skyphose/deckblock/photos/IMG_3814.jpeg

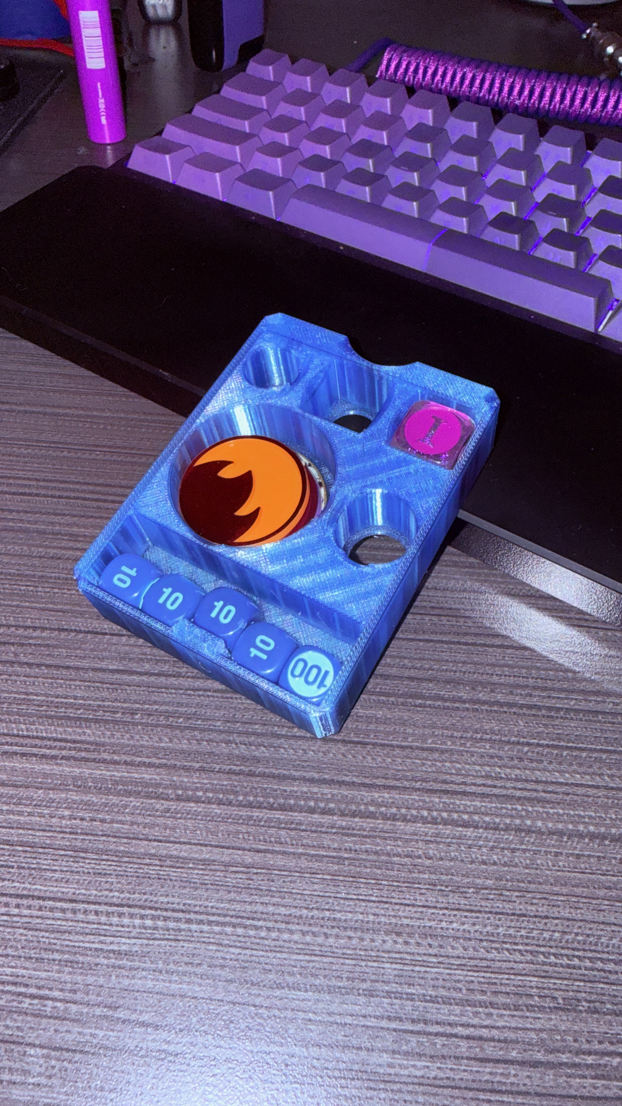
photos/IMG_3814.jpeg
