skyphose/deckblock/photos/IMG_3815.jpeg

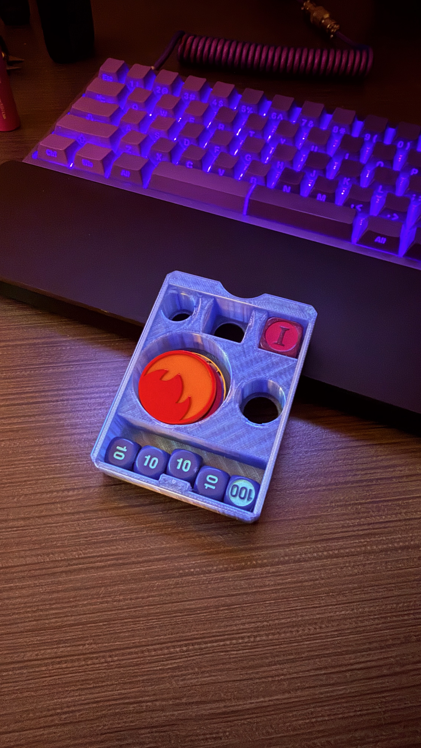
photos/IMG_3815.jpeg
