skyphose/deckblock/photos/IMG_3816.jpeg

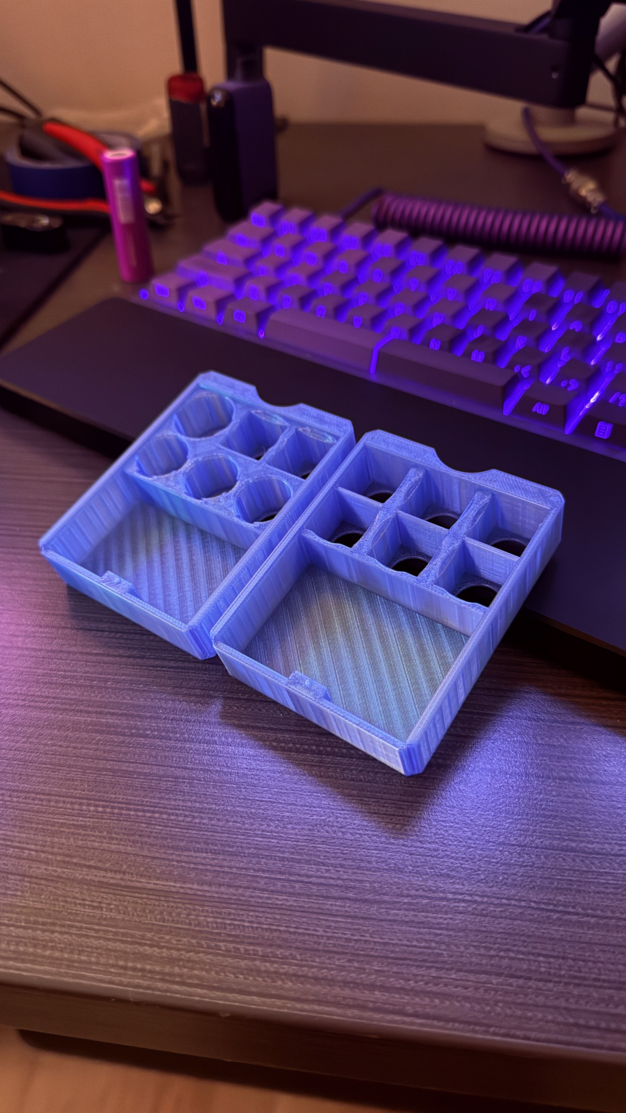
photos/IMG_3816.jpeg
