skyphose/deckblock/photos/IMG_3817.jpeg

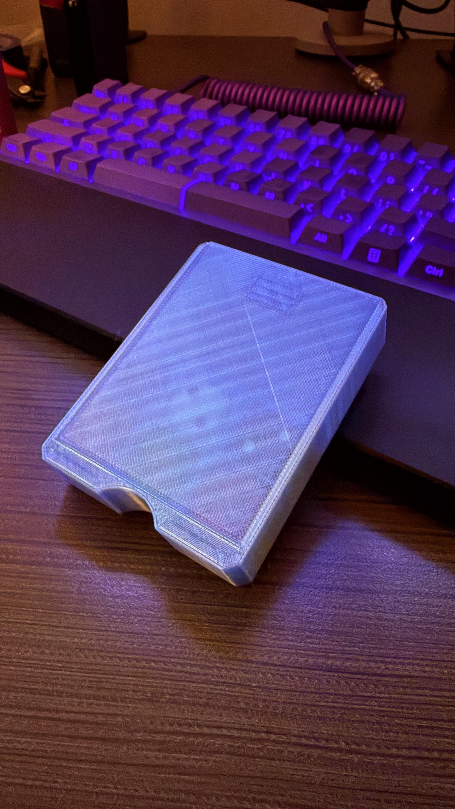
photos/IMG_3817.jpeg
