skyphose/deckblock/photos/IMG_3818.jpeg

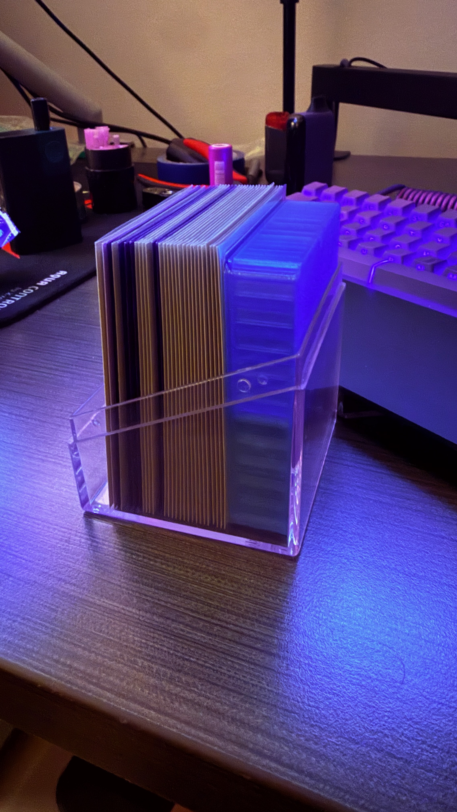
photos/IMG_3818.jpeg
