skyphose/deckblock/photos/IMG_3819.jpeg

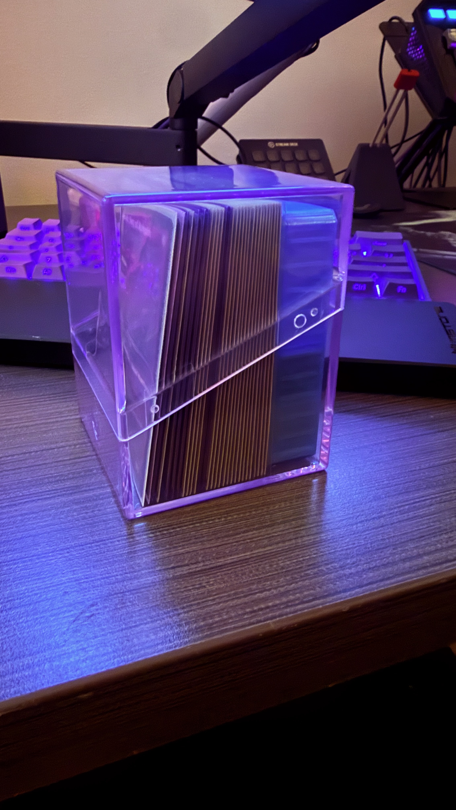
photos/IMG_3819.jpeg
