skyphose/deckblock/photos/IMG_3820.jpeg

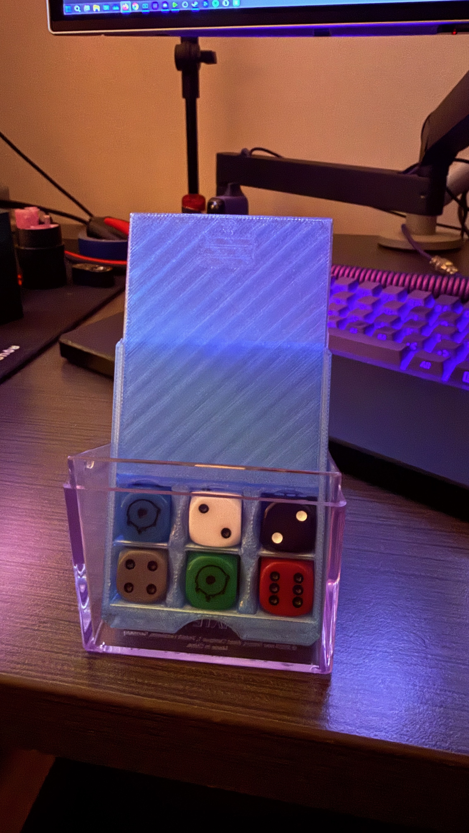
photos/IMG_3820.jpeg
