skyphose/deckblock/photos/IMG_3821.jpeg

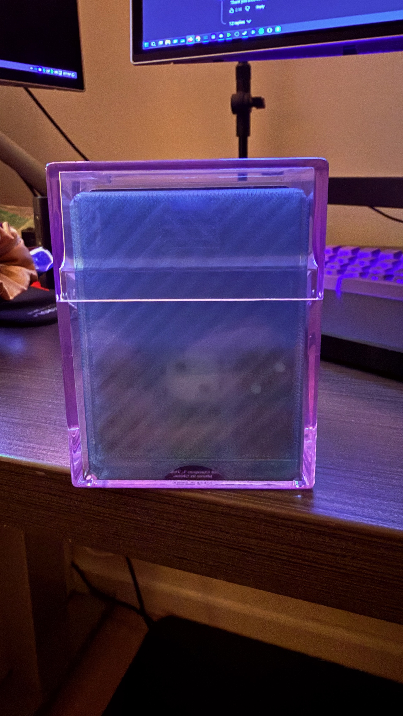
photos/IMG_3821.jpeg
