skyphose/deckblock/photos/IMG_3822.jpeg

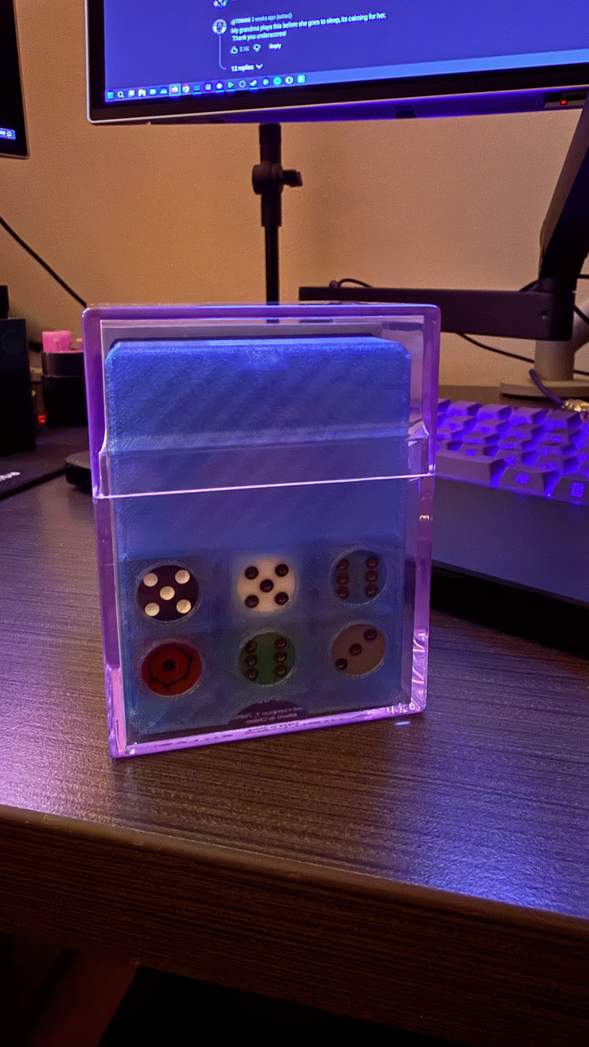
photos/IMG_3822.jpeg
